vrbq/tipe_ktane/bomb_defusal_game_v1/circuit/real/timer.JPG

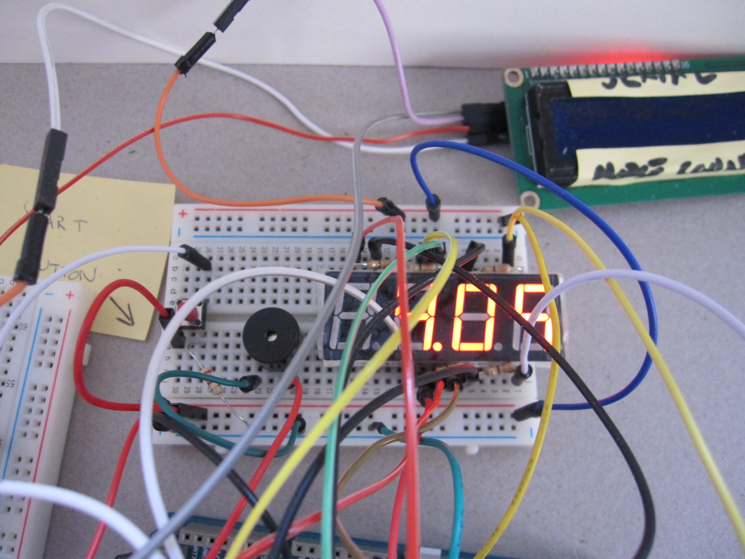
bomb_defusal_game_v1/circuit/real/timer.JPG
