vrbq/tipe_ktane/programme_arduino/timer/schema/timer.jpg

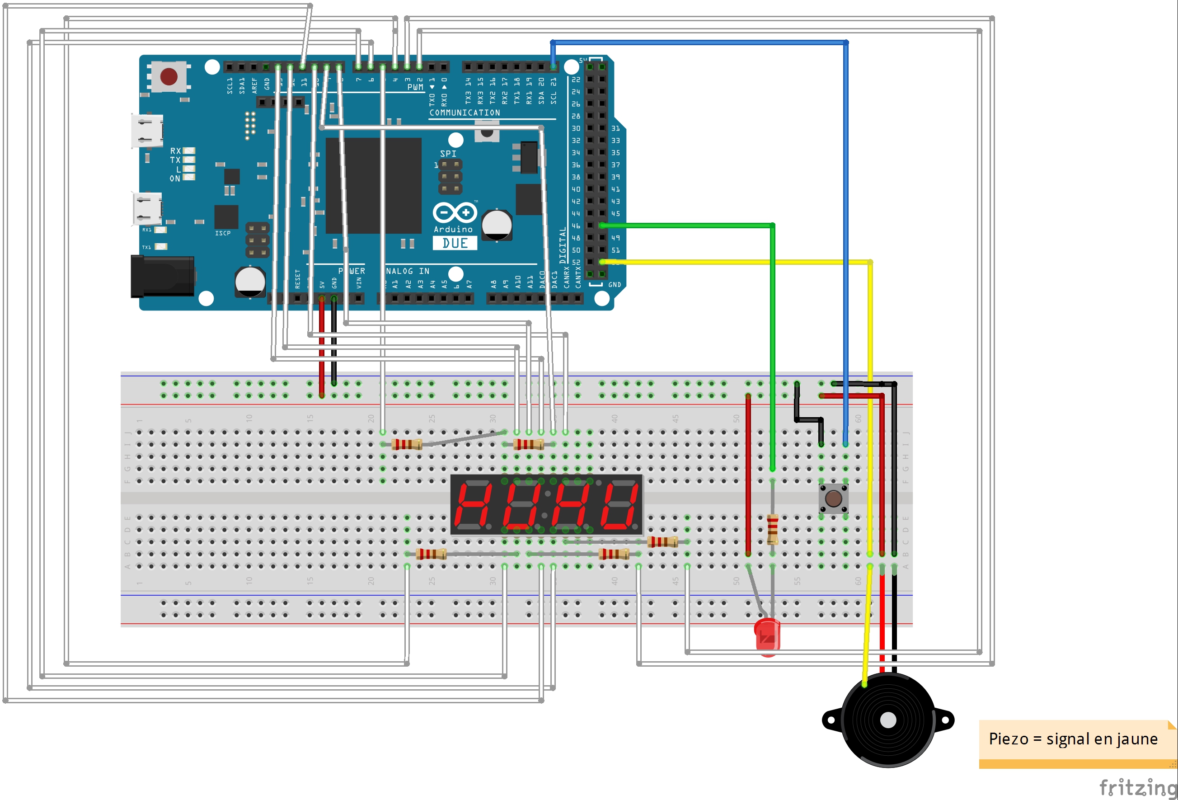
programme_arduino/timer/schema/timer.jpg
