vrbq/tipe_ktane/programme_arduino/keyboard_module/keyboard_module_due/circuit/component_list.png

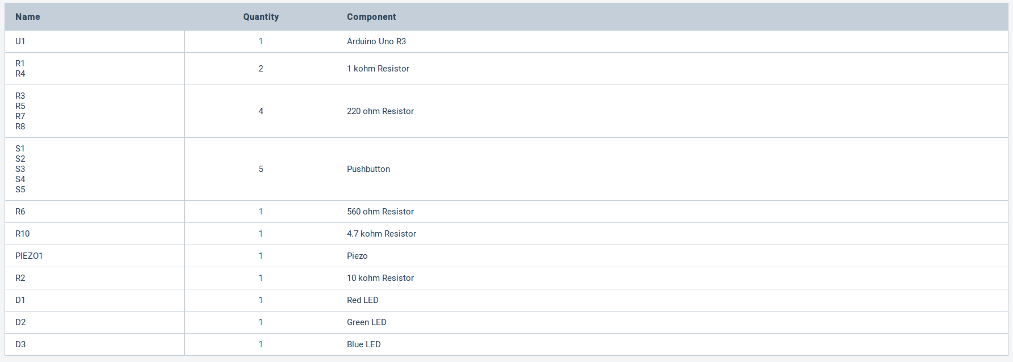
programme_arduino/keyboard_module/keyboard_module_due/circuit/component_list.png
