vrbq/tipe_ktane/programme_arduino/compilation/compilation.ino

// TIMER //
#include "SevSeg.h"

SevSeg sevseg;

//Connexions Ã©lectroniques et variables des boutons
const int BOUTON_START = 21;            // Le bouton START est reliÃ© Ã  la broche 21
int etatBoutonStart = 0;               // variable d'Ã©tat du bouton START

//Variables relatives au temps
unsigned long instantStart = 0;           // Instant ou l'on a appuyÃ© sur START
long tempsEcoule = 0;                     // Temps Ã©coulÃ© depuis que l'on a appuyÃ© sur START
long tps = 0;        

// MORSE//
const int led = 5;      // On attribue le pin sur lequel on a branché l'anode de la led  !!! IMPORTANT : On oublie pas de mettre une résistance !!!
const int led2 = 8;
const int temps = 250;   // Durée d'un point
int bouton = 7;
boolean erreur;
boolean module;
int buttonstate  = 0;
long alea;
int compteur;
String message = "";  // Ne pas mettre d'accent dans le message

void setup() {
  // TIMER //
  pinMode(BOUTON_START, INPUT);
  byte numDigits = 4;
  byte digitPins[] = {32, 33, 34, 35};
  byte segmentPins[] = {6, 7, 8, 9, 10, 11, 12, 13};
  sevseg.begin(COMMON_CATHODE, numDigits, digitPins, segmentPins);
  sevseg.setBrightness(90);

  //MORSE //
  module = false; 
  erreur = true;
  pinMode(bouton, INPUT);
  compteur = 0;
  Serial.begin(9600);
  Serial.print("hello world");
  randomSeed(analogRead(0));
  pinMode(led, OUTPUT); // On définit le pin "led" en sortie
  pinMode(led2, OUTPUT);
  alea = random(1,9);
  Serial.println(alea);
  switch (alea) {
    case 1:
      message = "TOTO";
      Serial.println(message);
      break;
    case 2:
      message = "CHIMIE";
      Serial.println(message);
      break;
    case 3:
      message = "TINTIN";
      Serial.println(message);
      break;
    case 4:
      message = "EPONGE";
      Serial.println(message);
      break;
    case 5:
      message = "MARTY";
      Serial.println(message);
      break;
    case 6:
      message = "MATHS";
      Serial.println(message);
      break;
    case 7:
      message = "PLAGE";
      Serial.println(message);
      break;
    case 8:
      message = "NEYMAR";
      Serial.println(message);
      break;
    case 9:
      message = "TIPE";
      Serial.println(message);
      break; 
  }

  // Ne pas modifier le code ci-dessous si vous ne savez pas ce que vous faites.
  
  message.toUpperCase();  // On transcrit tout le message en majuscule

  // On remplaceme chaque lettre du message par le code morse qui lui est attribué
  // Notez que j'ajoute un ";" volontairement à la fin afin de marquer la fin de la lettre dans le sequencage morse plus bas dans le code
  // on commence en toute logique par les "." et "-" et ";" qui sont dans votre message afin de ne pas remplacer les . ou - d'une lettre déjà convertie donc on commence par ça
  
  message.replace(".",".-.-.-;");
  message.replace("-","-....-;");
  // message.replace(";","-.-.-;");  // non je ne remplace pas celui là car ca enlèverait la fin des deux premières conversions
  message.replace("A",".-;");
  message.replace("B","-...;");
  message.replace("C","-.-.;");
  message.replace("D","-..;");
  message.replace("E",".;");
  message.replace("F","..-.;");
  message.replace("G","--.;");
  message.replace("H","....;");
  message.replace("I","..;");
  message.replace("J",".---;");
  message.replace("K","-.-;");
  message.replace("L",".-..;");
  message.replace("M","--;");
  message.replace("N","-.;");
  message.replace("O","---;");
  message.replace("P",".--.;");
  message.replace("Q","--.-;");
  message.replace("R",".-.;");
  message.replace("S","...;");
  message.replace("T","-;");
  message.replace("U","..-;");
  message.replace("V","...-;");
  message.replace("W",".--;");
  message.replace("X","-..-;");
  message.replace("Y","-.--;");
  message.replace("Z","--..;");
  message.replace("1",".----;");
  message.replace("2","..---;");
  message.replace("3","...--;");
  message.replace("4","....-;");
  message.replace("5",".....;");
  message.replace("6","-....;");
  message.replace("7","--...;");
  message.replace("8","---..;");
  message.replace("9","----.;");
  message.replace("0","-----;");
  message.replace(" ","|");           // Ici le "|" indique la fin d'un mot et qu'il peut y en avoir un autre derrière car il y a un espace dans votre message  
  message.replace(":","---...;");
  message.replace(",","--..--;");
  message.replace("?","..--..;");
  message.replace("'",".----.;");
  message.replace("!","-.-.--;");
  message.replace("@",".--.-.;");

  message = message + "|";  // J'ajoute un "|" qui marquera la fin du mot ou du message et qui servira dans le sequencage morse plus bas dans le code

  // On remplace maintenant ";|" par "|" dans le message transformé car la fin de lettre ne sert à rien avant un autre mot
  message.replace(";|","|");
  attachInterrupt(digitalPinToInterrupt(bouton), bascule, RISING);

}

void loop() {
  //TIMER//
//on commence par lire l'etat des buttons et stocker les Ã©tats dans les variables d'Ã©tat
  etatBoutonStart = digitalRead(BOUTON_START);
  
  //traitement bouton START
  if (etatBoutonStart == LOW) {
    tps = 300;                  // On met Ã  jour la variable Temps en fonction de la nouvelle valeur du compteur
    instantStart = millis();                                  //On utilise la fonction millis qui renvoie le nombre de millisecondes depuis que le programme est lancÃ© pour garder en mÃ©moire l'instant ou l'on a appuyÃ© sur start. Plus d'infos sur Millis ici : https://www.arduino.cc/en/Reference/Millis
    
    while (tempsEcoule != tps) {                            // Tant que le temps Ã©coulÃ© n'est pas celui que l'on a sÃ©lectionnÃ©
      tempsEcoule = 1 + (millis() - instantStart) / 1000;     //calcul du temps Ã©coulÃ© depuis l'appui sur start (+1 pour commencer chrono Ã  1)
      sevseg.setNumber(calcul_temps_restant(tempsEcoule), 2);// On calcule le temps qu'il reste Ã  dÃ©compter et on dÃ©finit ce temps l'afficheur 7 Segments
      sevseg.refreshDisplay();                                // On rafraichit l'afficheur 7 Segments
      
    }                                                        // Le temps Ã©coulÃ© est Ã©gal au temps sÃ©lectionnÃ© (La condition de la boucle while n'est plus vraie, donc on en sort)
    tempsEcoule = 0;
  }
  sevseg.refreshDisplay(); // Must run repeatedly
  
  //MORSE//
  if (module == true){
    digitalWrite(led2,HIGH);
  }
  else if (erreur == false){
    digitalWrite(led2,HIGH);
    delay(2000);
    digitalWrite(led2,LOW);
    
  } 
       SequencageMorse(message);   // On séquence notre message à la suite 


  
}

// FONTIONS ////////////////////////
// TIMER //
int calcul_temps_restant(int tempsActuel) {
  int tempsRestantEnMinutesEtSecondes=0;
  int minutesRestantes = (tps - tempsActuel) / 60;
  int secondesRestantes = (tps - tempsActuel) % 60;
  return tempsRestantEnMinutesEtSecondes = minutesRestantes * 100 + secondesRestantes;
}

// MORSE //

// Le séquencage morse
void SequencageMorse(String msg){
  // On crée une boucle FOR qui démarre à 0 jusqu'au nombre de lettre dans le message à séquencer en incrémentant de 1 à chaque tour
    for(int i = 0; i < msg.length(); i++) {
      // On vérifie à quoi correspond chaque caractère dans la boucle
      if (msg.substring(i, i+1) == "-" and module == false) {
        tiret();
      }
      else if (msg.substring(i, i+1) == "." and module == false) {
        point();
      }
      else if (msg.substring(i, i+1) == ";" and module == false) {
        delay(3*temps);  // Rapelez-vous, un espacement de la durée de 3 points entre chaque lettre
      }
      else if (msg.substring(i, i+1) == "|" and module == false) {
        Serial.print("   ");
        delay(7*temps);  // Rapelez-vous, un espacement de la durée de 7 points entre chaque mots
      }
  }
}
// Fonctions pour l'activation-désactivation de la led selon si c'est un tiret ou un point avec les temps qui leur sont attribué et que vous pouvez règler tout en haut au début du code qui est la variable "temps"
void tiret(){
  analogWrite(led,25);   // HIGH = Allumé
  delay(3*temps);
  digitalWrite(led, LOW);    // LOW = Eteind
  delay(temps);
}

void point(){
  analogWrite(led, 25);   // HIGH = Allumé
  delay(temps);
  digitalWrite(led, LOW);    // LOW = Eteind
  delay(temps);
}
void bascule(){ // c'est la fonction qui est déclanchée quand on appui sur le bouton grace a la foncion attachinterrupt
  compteur = compteur + 1;
  Serial.println(compteur);
  if (compteur == alea){
    module = true;
  }
  else if (compteur > alea){
    erreur = false;
  }
  
}
