vrbq/tipe_ktane/programme_arduino/compilation/keyboard_timer_2/keyboard_timer_2.ino

#include <AnalogMultiButton.h>
#include "KeyboardModule.h"
#include "CustomRandom.h"
#include "SevSeg.h"




//#define DEBUG

///////////// VARIABLES PROPRES AU JEU ///////////////
int bomb_explosed = 0;

unsigned long startMicros = 0; 
unsigned long currentMicros = micros();




///////////////// KEYBOARD //////////////////

int keyboard_toomanyerrors = 0;
int keyboard_solved = 0;

Keyboard keyboard;



///////////////////// TIMER /////////////
/*Connexions Ã©lectroniques et variables des boutons
const int button_timer_pin = A2;            
const int nb_button_timer = 5;
const int button_timer_values[nb_button_timer] = {512};
const int buttontimer1 = 0;
AnalogMultiButton button_timer(button_timer_pin, nb_button_timer, button_timer_values);*/

int etat_button_timer_pin = 0;               // variable d'Ã©tat du bouton START

//Variables relatives au temps
unsigned long instantStart_timer = 0;           // Instant ou l'on a appuyÃ© sur START
long tempsEcoule = 0;                     // Temps Ã©coulÃ© depuis que l'on a appuyÃ© sur START
long temps = 0;  

SevSeg sevseg; //7 segment du timer





//////////////////////////// SETUP /////////////////////////

void setup()
{
  
  //KEYBOARD
  Serial.begin(9600);
  randomSeed(analogRead(0));  

  //KEYBOARD
  keyboard = Keyboard(BUTTONS_TOTAL, SPEAKER_PIN, NUM_LEDS, LED_PINS);
  

  //TIMER 
  /*pinMode(button_timer_pin, INPUT);

  byte numDigits = 4;
  byte digitPins[] = {2, 3, 4, 5};
  byte segmentPins[] = {6, 7, 8, 9, 10, 11, 12, 13};
  sevseg.begin(COMMON_CATHODE, numDigits, digitPins, segmentPins);
  sevseg.setBrightness(90);*/
}


//////////////////////////// LOOP /////////////////////////

void loop()
{

  button_timer.update();
  

  //etat_button_timer_pin = digitalRead(button_timer_pin);

  if (button_timer.onPress(buttontimer1)) {
    temps = 60;                                               // Temps du compteur en secondes
    instantStart_timer = millis();                                  //On utilise la fonction millis qui renvoie le nombre de millisecondes depuis que le programme est lancÃ© pour garder en mÃ©moire l'instant ou l'on a appuyÃ© sur start. Plus d'infos sur Millis ici : https://www.arduino.cc/en/Reference/Millis
    
    while (tempsEcoule != temps && bomb_explosed == 0) {                            // Tant que le temps Ã©coulÃ© n'est pas celui que l'on a sÃ©lectionnÃ©
      tempsEcoule = 1 + (millis() - instantStart_timer) / 1000;     //calcul du temps Ã©coulÃ© depuis l'appui sur start (+1 pour commencer chrono Ã  1)
      sevseg.setNumber(calcul_temps_restant(tempsEcoule), 2);// On calcule le temps qu'il reste Ã  dÃ©compter et on dÃ©finit ce temps l'afficheur 7 Segments
      sevseg.refreshDisplay();                                // On rafraichit l'afficheur 7 Segments

      /////////// KEYBOARD MODULE /////////

      keyboard.update_keyboard();


      ////// COMPTEUR D'ERREUR TOTAL /////

      if (keyboard.error_count_keyboard_ == 3) //Penser a ajouter les erreurs des autres modules quand ils seront faits
      {
        Serial.println("You loose, too many errors.");
        bomb_explosed = 1;
        sevseg.setNumber(0, 2);
        sevseg.refreshDisplay();
      }
    
    }                                                      
    tempsEcoule = 0;
  }

sevseg.refreshDisplay(); // Must run repeatedly

#ifdef DEBUG
  if(button_keyboard.onPressAfter(4, 1500))
  {
    Serial.println("Reset button manually pressed");
    keyboard.reset();
  }
#endif

}




//////////// FONCTIONS ANNEXES //////////////////

  //////// TIMER /////
int calcul_temps_restant(int tempsActuel) {
  int tempsRestantEnMinutesEtSecondes=0;
  int minutesRestantes = (temps - tempsActuel) / 60;
  int secondesRestantes = (temps - tempsActuel) % 60;
  return tempsRestantEnMinutesEtSecondes = minutesRestantes * 100 + secondesRestantes;
}
