vrbq/tipe_ktane/programme_arduino/boutons/analog_multi_button_example/analog_multi_button_example.ino

// include the AnalogMultiButton library
#include <AnalogMultiButton.h>

// define the pin you want to use
const int BUTTONS_PIN = A8;

// set how many buttons you have connected
const int BUTTONS_TOTAL = 1;

// find out what the value of analogRead is when you press each of your buttons and put them in this array
// you can find this out by putting Serial.println(analogRead(BUTTONS_PIN)); in your loop() and opening the serial monitor to see the values
// make sure they are in order of smallest to largest
const int BUTTONS_VALUES[BUTTONS_TOTAL] = {512};

// you can also define constants for each of your buttons, which makes your code easier to read
// define these in the same order as the numbers in your BUTTONS_VALUES array, so whichever button has the smallest analogRead() number should come first
const int BUTTON_RED = 1;
const int BUTTON_GREEN = 0;
const int BUTTON_BLUE = 2;

// make an AnalogMultiButton object, pass in the pin, total and values array
AnalogMultiButton buttons(BUTTONS_PIN, BUTTONS_TOTAL, BUTTONS_VALUES);

// pass a fourth parameter to set the debounce time in milliseconds
// this defaults to 20 and can be increased if you're working with particularly bouncy buttons

void setup() {
  // begin serial so we can see which buttons are being pressed through the serial monitor
  Serial.begin(9600);
}

void loop() {
  //see which button are pressed
  //Serial.println(analogRead(BUTTONS_PIN));
  
  // update the AnalogMultiButton object every loop
  buttons.update();

  // check if BUTTON_RED is pressed
  if(buttons.isPressed(BUTTON_RED))
  {
    // Serial.println("Button red is pressed");
  } else {
    // Serial.println("Button red is not pressed");
  }

  // check if BUTTON_GREEN has just been pressed this update
  if(buttons.onPress(BUTTON_GREEN))
  {
    Serial.println("Green has been pressed");
  }

  // check if BUTTON_GREEN has just been released this update
  if(buttons.onRelease(BUTTON_GREEN))
  {
    Serial.println("Green has been released");
  }

  // do this if BUTTON_BLUE has been released
  if(buttons.onRelease(BUTTON_BLUE))
  {
    Serial.println("Blue has been released");
  }

  // do this once if BUTTON_BLUE has been held for 1 second
  if(buttons.onPressAfter(BUTTON_BLUE, 1000))
  {
    Serial.println("Blue has been down for 1 second");
  }

  // do this contantly if BUTTON_GREEN has been held down for less than a second
  if(buttons.isPressedBefore(BUTTON_GREEN, 1000))
  {
    Serial.print("Green is held for ");
    Serial.print(buttons.getPressDuration());
    Serial.println(" ms");
  }

  // do this contantly if BUTTON_RED has been held down for more than a second
  if(buttons.isPressedAfter(BUTTON_RED, 1000))
  {
    Serial.print("Red is held for ");
    Serial.print(buttons.getPressDuration());
    Serial.println(" ms");
  }

  // do this if BUTTON_BLUE was released, and it was held for 1 second or less
  if(buttons.onReleaseBefore(BUTTON_BLUE, 1000))
  {
    Serial.println("Blue has been released after less than 1 second of pressing");
    Serial.print("Blue was held for ");
    Serial.print(buttons.getLastReleasePressDuration());
    Serial.println(" ms");
  }

  // do this if BUTTON_BLUE was released, and it was held for 2 seconds or more
  if(buttons.onReleaseAfter(BUTTON_BLUE, 2000))
  {
    Serial.println("Blue has been released after at least 2 seconds of pressing");
    Serial.print("Blue was held for ");
    Serial.print(buttons.getLastReleasePressDuration());
    Serial.println(" ms");
  }

  //
  // More examples:
  //
  // do this once when BUTTON_BLUE is pressed, and again after 1 second
  // if(buttons.onPressAndAfter(BUTTON_BLUE, 1000)) {}
  //
  // do this once if BUTTON_BLUE is held for 1 second, and again every 0.5 seconds after that
  // if(buttons.onPressAfter(BUTTON_BLUE, 1000, 500)) {}
  //
  // do this once when BUTTON_BLUE is pressed, and again after 1 second, and again every 0.5 seconds after that
  // useful for cursors or scrolling through menu items
  // if(buttons.onPressAndAfter(BUTTON_BLUE, 1000, 500)) {}
  //

  delay(10);
}
